luiz-sene/pi3/PCI/pcb.png

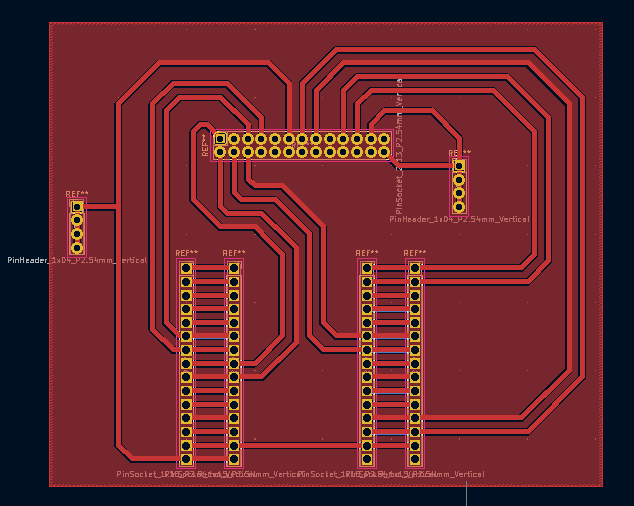
PCI/pcb.png
