luiz-sene/pi3/Programação/main/bt.h

#ifndef BT_H_INLCUDED
#define BT_H_INCLUDED

#include <stdio.h>
#include <stdlib.h>
#include <string.h>

#include "freertos/FreeRTOS.h"
#include "freertos/task.h"
#include "freertos/event_groups.h"
#include "esp_system.h"
#include "esp_log.h"
#include "nvs_flash.h"
#include "esp_bt.h"

#include "esp_gap_ble_api.h"
#include "esp_gatts_api.h"
#include "esp_bt_main.h"
#include "gatts_table_creat_demo.h"
#include "esp_gatt_common_api.h"


/* Attributes State Machine */
enum
{
    IDX_SVC,
    IDX_CHAR_A,
    IDX_CHAR_VAL_A,
    IDX_CHAR_CFG_A,

    IDX_CHAR_B,
    IDX_CHAR_VAL_B,

    IDX_CHAR_C,
    IDX_CHAR_VAL_C,

    HRS_IDX_NB,
};
typedef struct {
    uint8_t                 *prepare_buf;
    int                     prepare_len;
} prepare_type_env_t;

 prepare_type_env_t prepare_write_env;


void gatts_profile_event_handler(esp_gatts_cb_event_t event,
					esp_gatt_if_t gatts_if, esp_ble_gatts_cb_param_t *param);

void gap_event_handler(esp_gap_ble_cb_event_t event, esp_ble_gap_cb_param_t *param);
void example_prepare_write_event_env(esp_gatt_if_t gatts_if, prepare_type_env_t *prepare_write_env, esp_ble_gatts_cb_param_t *param);
void example_exec_write_event_env(prepare_type_env_t *prepare_write_env, esp_ble_gatts_cb_param_t *param);
void gatts_profile_event_handler(esp_gatts_cb_event_t event, esp_gatt_if_t gatts_if, esp_ble_gatts_cb_param_t *param);
void gatts_event_handler(esp_gatts_cb_event_t event, esp_gatt_if_t gatts_if, esp_ble_gatts_cb_param_t *param);

void rotina_bt(void);
#endif
